Dennis960/Blumy/Firmware/main/configuration_mode_server.c

#include "configuration_mode_server.h"

#include "esp_log.h"
#include "cJSON.h"

#include "plantfi.h"
#include "plantstore.h"
#include "peripherals/sensors.h"
#include "defaults.h"
#include "update.h"
#include "plantmqtt.h"
#include "plantnow.h"

#include "esp_https_ota.h"

#include "index_html.c"

float ota_update_percentage = -1;

// Returns the index_html from index_html.c
esp_err_t get_handler(httpd_req_t *req)
{
    httpd_resp_set_type(req, "text/html");
    httpd_resp_send(req, index_html, sizeof(index_html));
    return ESP_OK;
}

bool get_value(char *content, char *key, char *value, size_t value_size)
{
    // Request bodies are in the form of key=value\nkey2=value2\n
    char *key_start = strstr(content, key);
    if (key_start == NULL)
    {
        return false;
    }
    key_start += strlen(key) + 1;
    char *key_end = strstr(key_start, "\n");
    if (key_end == NULL)
    {
        return false;
    }
    size_t copy_len = key_end - key_start;
    if (copy_len >= value_size)
    {
        copy_len = value_size - 1;
    }
    strncpy(value, key_start, copy_len);
    value[copy_len] = '\0';
    ESP_LOGI("Configuration", "Extracted value for key '%s': '%s'", key, value);
    return true;
}

bool get_values(httpd_req_t *req, char *keys[], char *values[], size_t *sizes, int num_keys)
{
    char content[1000];
    size_t recv_size = MIN(req->content_len, sizeof(content) - 1);
    int ret = httpd_req_recv(req, content, recv_size);
    if (ret <= 0)
    {
        if (ret == HTTPD_SOCK_ERR_TIMEOUT)
        {
            httpd_resp_send_408(req);
        }
        return false;
    }
    content[ret] = '\0'; // Ensure null terminator
    for (int i = 0; i < num_keys; i++)
    {
        if (!get_value(content, keys[i], values[i], sizes[i]))
        {
            return false;
        }
    }
    return true;
}

bool get_single_value(httpd_req_t *req, char *value, size_t buffer_len)
{
    // The entire request body is the value, there is no key and no newline
    size_t recv_size = MIN(req->content_len, buffer_len - 1);
    int ret = httpd_req_recv(req, value, recv_size);
    if (ret <= 0)
    {
        if (ret == HTTPD_SOCK_ERR_TIMEOUT)
        {
            httpd_resp_send_408(req);
        }
        return false;
    }
    value[ret] = '\0'; // Ensure null terminator
    return true;
}

bool is_number(char *content)
{
    for (int i = 0; i < strlen(content); i++)
    {
        if (content[i] < '0' || content[i] > '9')
        {
            return false;
        }
    }
    return true;
}

esp_err_t post_api_connect_handler(httpd_req_t *req)
{
    char ssid[DEFAULT_SSID_MAX_LENGTH];
    char password[DEFAULT_PASSWORD_MAX_LENGTH];
    char *keys[] = {"ssid", "password"};
    char *values[] = {ssid, password};
    size_t sizes[] = {sizeof(ssid), sizeof(password)};
    if (!get_values(req, keys, values, sizes, 2))
    {
        return ESP_FAIL;
    }

    httpd_resp_send(req, "OK", HTTPD_RESP_USE_STRLEN);

    plantfi_configureSta(ssid, password, 5, true);
    return ESP_OK;
}

esp_err_t post_api_reset_handler(httpd_req_t *req)
{
    httpd_resp_send(req, "OK", HTTPD_RESP_USE_STRLEN);

    sensors_playShutdownSound();
    esp_restart();
    return ESP_OK;
}

esp_err_t get_api_networks_handler(httpd_req_t *req)
{
    plantfi_ap_record_t ap_records[20];
    int num_ap_records = 20;
    plantfi_scan_networks(ap_records, &num_ap_records);

    cJSON *root = cJSON_CreateArray();
    for (int i = 0; i < num_ap_records; i++)
    {
        cJSON *ap = cJSON_CreateObject();
        cJSON_AddNumberToObject(ap, "rssi", ap_records[i].rssi);
        cJSON_AddStringToObject(ap, "ssid", ap_records[i].ssid);
        cJSON_AddNumberToObject(ap, "secure", ap_records[i].secure);
        cJSON_AddItemToArray(root, ap);
    }

    char *resp = cJSON_Print(root);
    cJSON_Delete(root);

    httpd_resp_set_type(req, "application/json");
    httpd_resp_send(req, resp, HTTPD_RESP_USE_STRLEN);
    free(resp);
    return ESP_OK;
}

esp_err_t get_api_isConnected_handler(httpd_req_t *req)
{
    plantfi_sta_status_t status = plantfi_get_sta_status();
    char resp[2];
    sprintf(resp, "%d", status);
    httpd_resp_send(req, resp, HTTPD_RESP_USE_STRLEN);
    return ESP_OK;
}

esp_err_t post_api_cloudSetup_mqtt_handler(httpd_req_t *req)
{
    char sensorId[100];
    char server[100];
    char portString[10];
    char username[100];
    char password[100];
    char topic[100];
    char clientId[100];
    char *keys[] = {"sensorId", "server", "port", "username", "password", "topic", "clientId"};
    char *values[] = {sensorId, server, portString, username, password, topic, clientId};
    size_t sizes[] = {sizeof(sensorId), sizeof(server), sizeof(portString), sizeof(username), sizeof(password), sizeof(topic), sizeof(clientId)};
    if (!get_values(req, keys, values, sizes, 7) || !is_number(portString))
    {
        return ESP_FAIL;
    }

    uint32_t port = atoi(portString);

    plantstore_setCloudConfigurationMqtt(sensorId, server, port, username, password, topic, clientId);
    plantmqtt_homeassistant_create_sensor();

    httpd_resp_send(req, "OK", HTTPD_RESP_USE_STRLEN);
    return ESP_OK;
}

esp_err_t post_api_cloudSetup_http_handler(httpd_req_t *req)
{
    char sensorId[100];
    char url[100];
    char auth[100];
    char *keys[] = {"sensorId", "url", "auth"};
    char *values[] = {sensorId, url, auth};
    size_t sizes[] = {sizeof(sensorId), sizeof(url), sizeof(auth)};
    if (!get_values(req, keys, values, sizes, 3))
    {
        return ESP_FAIL;
    }

    plantstore_setCloudConfigurationHttp(sensorId, url, auth);

    httpd_resp_send(req, "OK", HTTPD_RESP_USE_STRLEN);
    return ESP_OK;
}

esp_err_t post_api_cloudSetup_blumy_handler(httpd_req_t *req)
{
    char token[100];
    char url[100];
    char *keys[] = {"token", "url"};
    char *values[] = {token, url};
    size_t sizes[] = {sizeof(token), sizeof(url)};
    if (!get_values(req, keys, values, sizes, 2))
    {
        return ESP_FAIL;
    }

    plantstore_setCloudConfigurationBlumy(token, url);

    httpd_resp_send(req, "OK", HTTPD_RESP_USE_STRLEN);
    return ESP_OK;
}

esp_err_t get_api_cloudSetup_mqtt_handler(httpd_req_t *req)
{
    char sensorId[100];
    char server[100];
    uint32_t port;
    char username[100];
    char password[100];
    char topic[100];
    char clientId[100];

    if (!plantstore_getCloudConfigurationMqtt(sensorId, server, &port, username, password, topic, clientId, sizeof(sensorId), sizeof(server), sizeof(username), sizeof(password), sizeof(topic), sizeof(clientId)))
    {
        httpd_resp_send_404(req);
        return ESP_FAIL;
    }

    cJSON *root = cJSON_CreateObject();
    cJSON_AddStringToObject(root, "sensorId", sensorId);
    cJSON_AddStringToObject(root, "server", server);
    cJSON_AddNumberToObject(root, "port", port);
    cJSON_AddStringToObject(root, "username", username);
    cJSON_AddStringToObject(root, "password", password);
    cJSON_AddStringToObject(root, "topic", topic);
    cJSON_AddStringToObject(root, "clientId", clientId);

    char *resp = cJSON_Print(root);
    cJSON_Delete(root);

    httpd_resp_set_type(req, "application/json");
    httpd_resp_send(req, resp, HTTPD_RESP_USE_STRLEN);
    free(resp);
    return ESP_OK;
}

esp_err_t get_api_cloudSetup_http_handler(httpd_req_t *req)
{
    char sensorId[100];
    char url[100];
    char auth[100];

    if (!plantstore_getCloudConfigurationHttp(sensorId, url, auth, sizeof(sensorId), sizeof(url), sizeof(auth)))
    {
        httpd_resp_send_404(req);
        return ESP_FAIL;
    }

    cJSON *root = cJSON_CreateObject();
    cJSON_AddStringToObject(root, "sensorId", sensorId);
    cJSON_AddStringToObject(root, "url", url);
    cJSON_AddStringToObject(root, "auth", auth);

    char *resp = cJSON_Print(root);
    cJSON_Delete(root);

    httpd_resp_set_type(req, "application/json");
    httpd_resp_send(req, resp, HTTPD_RESP_USE_STRLEN);
    free(resp);
    return ESP_OK;
}

esp_err_t get_api_cloudSetup_blumy_handler(httpd_req_t *req)
{
    char token[100] = "";
    char url[100] = DEFAULT_API_URL;

    plantstore_getCloudConfigurationBlumy(token, url, sizeof(token), sizeof(url));

    cJSON *root = cJSON_CreateObject();
    cJSON_AddStringToObject(root, "token", token);
    cJSON_AddStringToObject(root, "url", url);

    char *resp = cJSON_Print(root);
    cJSON_Delete(root);

    httpd_resp_send(req, resp, HTTPD_RESP_USE_STRLEN);
    free(resp);
    return ESP_OK;
}

esp_err_t post_api_cloudTest_mqtt_handler(httpd_req_t *req)
{
    char sensorId[100];
    char server[100];
    char portString[10];
    char username[100];
    char password[100];
    char topic[100];
    char clientId[100];

    char *keys[] = {"sensorId", "server", "port", "username", "password", "topic", "clientId"};
    char *values[] = {sensorId, server, portString, username, password, topic, clientId};
    size_t sizes[] = {sizeof(sensorId), sizeof(server), sizeof(portString), sizeof(username), sizeof(password), sizeof(topic), sizeof(clientId)};
    if (!get_values(req, keys, values, sizes, 7) || !is_number(portString))
    {
        return ESP_FAIL;
    }

    uint32_t port = atoi(portString);

    const bool connectionOk = plantfi_test_mqtt_connection(sensorId, server, port, username, password, topic, clientId);
    char resp[6];
    sprintf(resp, "%s", connectionOk ? "true" : "false");
    httpd_resp_send(req, resp, HTTPD_RESP_USE_STRLEN);
    return ESP_OK;
}
esp_err_t post_api_cloudTest_http_handler(httpd_req_t *req)
{
    char sensorId[100];
    char url[100];
    char auth[100];

    char *keys[] = {"sensorId", "url", "auth"};
    char *values[] = {sensorId, url, auth};
    size_t sizes[] = {sizeof(sensorId), sizeof(url), sizeof(auth)};
    if (!get_values(req, keys, values, sizes, 3))
    {
        return ESP_FAIL;
    }

    const bool connectionOk = plantfi_test_http_connection(sensorId, url, auth);
    char resp[6];
    sprintf(resp, "%s", connectionOk ? "true" : "false");
    httpd_resp_send(req, resp, HTTPD_RESP_USE_STRLEN);
    return ESP_OK;
}
esp_err_t post_api_cloudTest_blumy_handler(httpd_req_t *req)
{
    char token[100];
    char url[100];
    char *keys[] = {"token", "url"};
    char *values[] = {token, url};
    size_t sizes[] = {sizeof(token), sizeof(url)};
    if (!get_values(req, keys, values, sizes, 2))
    {
        return ESP_FAIL;
    }

    const bool connectionOk = plantfi_test_blumy_connection(token, url);
    char resp[6];
    sprintf(resp, "%s", connectionOk ? "true" : "false");
    httpd_resp_send(req, resp, HTTPD_RESP_USE_STRLEN);
    return ESP_OK;
}

esp_err_t post_api_cloudDisable_mqtt_handler(httpd_req_t *req)
{
    plantstore_resetCloudConfigurationMqtt();
    httpd_resp_send(req, "OK", HTTPD_RESP_USE_STRLEN);
    return ESP_OK;
}

esp_err_t post_api_cloudDisable_http_handler(httpd_req_t *req)
{
    plantstore_resetCloudConfigurationHttp();
    httpd_resp_send(req, "OK", HTTPD_RESP_USE_STRLEN);
    return ESP_OK;
}

esp_err_t post_api_cloudDisable_blumy_handler(httpd_req_t *req)
{
    plantstore_resetCloudConfigurationBlumy();
    httpd_resp_send(req, "OK", HTTPD_RESP_USE_STRLEN);
    return ESP_OK;
}

esp_err_t post_api_timeouts_sleep_handler(httpd_req_t *req)
{
    char timoutString[10];
    if (!get_single_value(req, timoutString, 10) || !is_number(timoutString))
    {
        return ESP_FAIL;
    }

    int32_t timeout;
    sscanf(timoutString, "%ld", &timeout);

    plantstore_setSensorTimeoutSleepMs(timeout);

    httpd_resp_send(req, "OK", HTTPD_RESP_USE_STRLEN);
    return ESP_OK;
}

esp_err_t get_api_timeouts_sleep_handler(httpd_req_t *req)
{
    uint64_t timeout = DEFAULT_SENSOR_TIMEOUT_SLEEP_MS;
    plantstore_getSensorTimeoutSleepMs(&timeout);

    char resp[15];
    sprintf(resp, "%llu", timeout);
    httpd_resp_send(req, resp, HTTPD_RESP_USE_STRLEN);
    return ESP_OK;
}

esp_err_t get_api_timeouts_configurationMode_handler(httpd_req_t *req)
{
    int32_t timeout = DEFAULT_CONFIGURATION_MODE_TIMEOUT_MS;
    plantstore_getConfigurationModeTimeoutMs(&timeout);

    char resp[15];
    sprintf(resp, "%ld", timeout);
    httpd_resp_send(req, resp, HTTPD_RESP_USE_STRLEN);
    return ESP_OK;
}

esp_err_t post_api_timeouts_configurationMode_handler(httpd_req_t *req)
{
    char timoutString[10];
    if (!get_single_value(req, timoutString, 10) || !is_number(timoutString))
    {
        return ESP_FAIL;
    }

    int32_t timeout;
    sscanf(timoutString, "%ld", &timeout);

    plantstore_setConfigurationModeTimeoutMs(timeout);

    httpd_resp_send(req, "OK", HTTPD_RESP_USE_STRLEN);
    return ESP_OK;
}

esp_err_t get_api_timeouts_wdt_handler(httpd_req_t *req)
{
    uint64_t timeout = DEFAULT_WATCHDOG_TIMEOUT_MS;
    plantstore_getWatchdogTimeoutMs(&timeout);

    char resp[15];
    sprintf(resp, "%llu", timeout);
    httpd_resp_send(req, resp, HTTPD_RESP_USE_STRLEN);
    return ESP_OK;
}

esp_err_t post_api_timeouts_wdt_handler(httpd_req_t *req)
{
    char timoutString[10];
    if (!get_single_value(req, timoutString, 10) || !is_number(timoutString))
    {
        return ESP_FAIL;
    }

    uint64_t timeout;
    sscanf(timoutString, "%llu", &timeout);

    plantstore_setWatchdogTimeoutMs(timeout);

    httpd_resp_send(req, "OK", HTTPD_RESP_USE_STRLEN);
    return ESP_OK;
}

esp_err_t get_api_timeouts_mqtt_message_handler(httpd_req_t *req)
{
    uint64_t timeout = DEFAULT_MQTT_MESSAGE_TIMEOUT_MS;
    plantstore_getMqttMessageTimeoutMs(&timeout);

    char resp[15];
    sprintf(resp, "%llu", timeout);
    httpd_resp_send(req, resp, HTTPD_RESP_USE_STRLEN);
    return ESP_OK;
}

esp_err_t post_api_timeouts_mqtt_message_handler(httpd_req_t *req)
{
    char timoutString[10];
    if (!get_single_value(req, timoutString, 10) || !is_number(timoutString))
    {
        return ESP_FAIL;
    }

    uint64_t timeout;
    sscanf(timoutString, "%llu", &timeout);

    plantstore_setMqttMessageTimeoutMs(timeout);

    httpd_resp_send(req, "OK", HTTPD_RESP_USE_STRLEN);
    return ESP_OK;
}

esp_err_t get_api_led_brightness_handler(httpd_req_t *req)
{
    uint8_t brightness = DEFAULT_LED_BRIGHTNESS;
    plantstore_getLedBrightness(&brightness);

    char resp[4];
    sprintf(resp, "%d", brightness);
    httpd_resp_send(req, resp, HTTPD_RESP_USE_STRLEN);
    return ESP_OK;
}

esp_err_t post_api_led_brightness_handler(httpd_req_t *req)
{
    char brightnessString[10];
    if (!get_single_value(req, brightnessString, 10))
    {
        ESP_LOGI("DEBUG", "1");
        return ESP_FAIL;
    }
    ESP_LOGI("DEBUG", "%s", brightnessString);
    if (!is_number(brightnessString))
    {
        ESP_LOGI("DEBUG", "2");
        return ESP_FAIL;
    }

    uint8_t brightness;
    sscanf(brightnessString, "%hhu", &brightness);

    plantstore_setLedBrightness(brightness);

    httpd_resp_send(req, "OK", HTTPD_RESP_USE_STRLEN);
    return ESP_OK;
}

esp_err_t get_api_update_percentage_handler(httpd_req_t *req)
{
    char resp[10];
    sprintf(resp, "%.2f", ota_update_percentage);
    httpd_resp_send(req, resp, HTTPD_RESP_USE_STRLEN);
    return ESP_OK;
}

esp_err_t get_api_connectedNetwork_handler(httpd_req_t *req)
{
    char ssid[DEFAULT_SSID_MAX_LENGTH];
    char password[DEFAULT_PASSWORD_MAX_LENGTH];

    if (!plantstore_getWifiCredentials(ssid, password, sizeof(ssid), sizeof(password)))
    {
        httpd_resp_send_404(req);
        return ESP_FAIL;
    }
    plantfi_sta_status_t status = plantfi_get_sta_status();
    int8_t rssi = plantfi_getRssi();

    cJSON *root = cJSON_CreateObject();
    cJSON_AddStringToObject(root, "ssid", ssid);
    // cJSON_AddStringToObject(root, "password", password);
    cJSON_AddNumberToObject(root, "status", status);
    cJSON_AddNumberToObject(root, "rssi", rssi);

    char *resp = cJSON_Print(root);
    cJSON_Delete(root);

    httpd_resp_set_type(req, "application/json");
    httpd_resp_send(req, resp, HTTPD_RESP_USE_STRLEN);
    free(resp);
    return ESP_OK;
}

esp_err_t get_api_sensor_data_handler(httpd_req_t *req)
{
    sensors_full_data_t sensors_data;
    sensors_full_read(&sensors_data);

    cJSON *root = cJSON_CreateObject();
    cJSON_AddNumberToObject(root, "temperature", sensors_data.temperature);
    cJSON_AddNumberToObject(root, "humidity", sensors_data.humidity);
    cJSON_AddNumberToObject(root, "light", sensors_data.light);
    cJSON_AddNumberToObject(root, "moisture", sensors_data.moisture_measurement);
    cJSON_AddNumberToObject(root, "voltage", sensors_data.voltage);

    char *resp = cJSON_Print(root);
    cJSON_Delete(root);

    httpd_resp_set_type(req, "application/json");
    httpd_resp_send(req, resp, HTTPD_RESP_USE_STRLEN);
    free(resp);
    return ESP_OK;
}

esp_err_t post_api_factoryReset_handler(httpd_req_t *req)
{
    httpd_resp_send(req, "OK", HTTPD_RESP_USE_STRLEN);

    plantstore_factoryReset();
    esp_restart();
    return ESP_OK;
}

esp_err_t post_api_update_firmware_handler(httpd_req_t *req)
{
    char url[100];
    char *keys[] = {"url"};
    char *values[] = {url};
    size_t sizes[] = {sizeof(url)};
    if (!get_values(req, keys, values, sizes, 1))
    {
        return ESP_FAIL;
    }

    plantstore_setFirmwareUpdateUrl(url);
    ota_update_percentage = 0;

    httpd_resp_send(req, "OK", HTTPD_RESP_USE_STRLEN);
    update_updateFirmware(&ota_update_percentage);
    return ESP_OK;
}

esp_err_t get_api_update_firmware_handler(httpd_req_t *req)
{
    char url[100] = DEFAULT_FIRMWARE_UPDATE_URL;
    plantstore_getFirmwareUpdateUrl(url, sizeof(url));

    cJSON *root = cJSON_CreateObject();
    cJSON_AddStringToObject(root, "url", url);

    char *resp = cJSON_Print(root);
    cJSON_Delete(root);

    httpd_resp_set_type(req, "application/json");
    httpd_resp_send(req, resp, HTTPD_RESP_USE_STRLEN);
    free(resp);
    return ESP_OK;
}

esp_err_t post_api_update_check_handler(httpd_req_t *req)
{
    char url[100];
    char *keys[] = {"url"};
    char *values[] = {url};
    size_t sizes[] = {sizeof(url)};
    if (!get_values(req, keys, values, sizes, 1))
    {
        return ESP_FAIL;
    }

    esp_http_client_config_t config = {
        .url = url,
        .method = HTTP_METHOD_HEAD,
        .timeout_ms = 10000,
        .cert_pem = NULL,
    };
    esp_http_client_handle_t client = esp_http_client_init(&config);
    if (client == NULL)
    {
        ESP_LOGE("HTTP", "Failed to initialize HTTP client");
        return ESP_FAIL;
    }
    esp_err_t err = esp_http_client_perform(client);
    if (err != ESP_OK)
    {
        ESP_LOGE("HTTP", "Failed to perform HTTP request (%s)", esp_err_to_name(err));
        return err;
    }
    int status_code = esp_http_client_get_status_code(client);
    int content_length = esp_http_client_get_content_length(client);
    ESP_LOGI("HTTP", "Status code: %d, Content length: %d", status_code, content_length);

    char resp[6];
    sprintf(resp, "%s", status_code == 200 ? "true" : "false");
    httpd_resp_send(req, resp, HTTPD_RESP_USE_STRLEN);

    esp_http_client_cleanup(client);
    return ESP_OK;
}

esp_err_t get_api_firmware_version_handler(httpd_req_t *req)
{
    uint64_t version = FIRMWARE_VERSION;
    char resp[20];
    sprintf(resp, "%llu", version);
    httpd_resp_send(req, resp, HTTPD_RESP_USE_STRLEN);
    return ESP_OK;
}

esp_err_t plantnow_hasReceivedPeerMacHandler(httpd_req_t *req)
{
    uint8_t *mac = plantnow_getPeerMac();
    char resp[20]; // Enough for "xx:xx:xx:xx:xx:xx"
    if (mac == NULL)
    {
        sprintf(resp, "\"\"");
    }
    else
    {
        sprintf(resp, "\"%02x:%02x:%02x:%02x:%02x:%02x\"",
                mac[0], mac[1], mac[2], mac[3], mac[4], mac[5]);
    }
    httpd_resp_set_type(req, "application/json");
    httpd_resp_send(req, resp, HTTPD_RESP_USE_STRLEN);
    return ESP_OK;
}

esp_err_t plantnow_sendWifiCredentialsHandler(httpd_req_t *req)
{
    if (plantnow_getPeerMac() == NULL)
    {
        httpd_resp_send_err(req, HTTPD_500_INTERNAL_SERVER_ERROR, "ERROR: No peer MAC address received");
        return ESP_FAIL;
    }
    if (!plantstore_getWifiCredentials(NULL, NULL, 0, 0))
    {
        httpd_resp_send_err(req, HTTPD_500_INTERNAL_SERVER_ERROR, "ERROR: No WiFi credentials stored");
        return ESP_FAIL;
    }
    if (plantnow_sendWifiCredentials(true) != ESP_OK)
    {
        httpd_resp_send_err(req, HTTPD_500_INTERNAL_SERVER_ERROR, "ERROR: Failed to send WiFi credentials");
        return ESP_FAIL;
    }

    httpd_resp_send(req, "OK", HTTPD_RESP_USE_STRLEN);
    return ESP_OK;
}

esp_err_t plantnow_sendCloudSetup_blumyHandler(httpd_req_t *req)
{
    char token[100];
    char url[100];
    char *keys[] = {"token", "url"};
    char *values[] = {token, url};
    size_t sizes[] = {sizeof(token), sizeof(url)};
    if (!get_values(req, keys, values, sizes, 2))
    {
        return ESP_FAIL;
    }
    if (plantnow_getPeerMac() == NULL)
    {
        httpd_resp_send_err(req, HTTPD_500_INTERNAL_SERVER_ERROR, "ERROR: No peer MAC address received");
        return ESP_FAIL;
    }
    cloud_setup_blumy_t setup;
    strcpy(setup.token, token);
    strcpy(setup.url, url);
    if (plantnow_sendCloudSetupBlumy(&setup, true) != ESP_OK)
    {
        httpd_resp_send_err(req, HTTPD_500_INTERNAL_SERVER_ERROR, "ERROR: Failed to send Blumy cloud setup");
        return ESP_FAIL;
    }

    httpd_resp_send(req, "OK", HTTPD_RESP_USE_STRLEN);
    return ESP_OK;
}

httpd_uri_t post_api_connect = {
    .uri = "/api/connect",
    .method = HTTP_POST,
    .handler = post_api_connect_handler,
    .user_ctx = NULL};

httpd_uri_t post_api_reset = {
    .uri = "/api/reset",
    .method = HTTP_POST,
    .handler = post_api_reset_handler,
    .user_ctx = NULL};

httpd_uri_t get_api_networks = {
    .uri = "/api/networks",
    .method = HTTP_GET,
    .handler = get_api_networks_handler,
    .user_ctx = NULL};

httpd_uri_t get_api_isConnected = {
    .uri = "/api/isConnected",
    .method = HTTP_GET,
    .handler = get_api_isConnected_handler,
    .user_ctx = NULL};

httpd_uri_t post_api_cloudSetup_mqtt = {
    .uri = "/api/cloudSetup/mqtt",
    .method = HTTP_POST,
    .handler = post_api_cloudSetup_mqtt_handler,
    .user_ctx = NULL};
httpd_uri_t post_api_cloudSetup_http = {
    .uri = "/api/cloudSetup/http",
    .method = HTTP_POST,
    .handler = post_api_cloudSetup_http_handler,
    .user_ctx = NULL};
httpd_uri_t post_api_cloudSetup_blumy = {
    .uri = "/api/cloudSetup/blumy",
    .method = HTTP_POST,
    .handler = post_api_cloudSetup_blumy_handler,
    .user_ctx = NULL};

httpd_uri_t get_api_cloudSetup_mqtt = {
    .uri = "/api/cloudSetup/mqtt",
    .method = HTTP_GET,
    .handler = get_api_cloudSetup_mqtt_handler,
    .user_ctx = NULL};
httpd_uri_t get_api_cloudSetup_http = {
    .uri = "/api/cloudSetup/http",
    .method = HTTP_GET,
    .handler = get_api_cloudSetup_http_handler,
    .user_ctx = NULL};
httpd_uri_t get_api_cloudSetup_blumy = {
    .uri = "/api/cloudSetup/blumy",
    .method = HTTP_GET,
    .handler = get_api_cloudSetup_blumy_handler,
    .user_ctx = NULL};

httpd_uri_t post_api_cloudTest_mqtt = {
    .uri = "/api/cloudTest/mqtt",
    .method = HTTP_POST,
    .handler = post_api_cloudTest_mqtt_handler,
    .user_ctx = NULL};
httpd_uri_t post_api_cloudTest_http = {
    .uri = "/api/cloudTest/http",
    .method = HTTP_POST,
    .handler = post_api_cloudTest_http_handler,
    .user_ctx = NULL};
httpd_uri_t post_api_cloudTest_blumy = {
    .uri = "/api/cloudTest/blumy",
    .method = HTTP_POST,
    .handler = post_api_cloudTest_blumy_handler,
    .user_ctx = NULL};

httpd_uri_t post_api_cloudDisable_mqtt = {
    .uri = "/api/cloudDisable/mqtt",
    .method = HTTP_POST,
    .handler = post_api_cloudDisable_mqtt_handler,
    .user_ctx = NULL};
httpd_uri_t post_api_cloudDisable_http = {
    .uri = "/api/cloudDisable/http",
    .method = HTTP_POST,
    .handler = post_api_cloudDisable_http_handler,
    .user_ctx = NULL};
httpd_uri_t post_api_cloudDisable_blumy = {
    .uri = "/api/cloudDisable/blumy",
    .method = HTTP_POST,
    .handler = post_api_cloudDisable_blumy_handler,
    .user_ctx = NULL};

httpd_uri_t post_api_timeouts_sleep = {
    .uri = "/api/timeouts/sleep",
    .method = HTTP_POST,
    .handler = post_api_timeouts_sleep_handler,
    .user_ctx = NULL};

httpd_uri_t get_api_timeouts_sleep = {
    .uri = "/api/timeouts/sleep",
    .method = HTTP_GET,
    .handler = get_api_timeouts_sleep_handler,
    .user_ctx = NULL};

httpd_uri_t get_api_timeouts_configurationMode = {
    .uri = "/api/timeouts/configurationMode",
    .method = HTTP_GET,
    .handler = get_api_timeouts_configurationMode_handler,
    .user_ctx = NULL};

httpd_uri_t post_api_timeouts_configurationMode = {
    .uri = "/api/timeouts/configurationMode",
    .method = HTTP_POST,
    .handler = post_api_timeouts_configurationMode_handler,
    .user_ctx = NULL};

httpd_uri_t get_api_timeouts_wdt = {
    .uri = "/api/timeouts/wdt",
    .method = HTTP_GET,
    .handler = get_api_timeouts_wdt_handler,
    .user_ctx = NULL};

httpd_uri_t post_api_timeouts_wdt = {
    .uri = "/api/timeouts/wdt",
    .method = HTTP_POST,
    .handler = post_api_timeouts_wdt_handler,
    .user_ctx = NULL};

httpd_uri_t get_api_timeouts_mqtt_message = {
    .uri = "/api/timeouts/mqttMessage",
    .method = HTTP_GET,
    .handler = get_api_timeouts_mqtt_message_handler,
    .user_ctx = NULL};

httpd_uri_t post_api_timeouts_mqtt_message = {
    .uri = "/api/timeouts/mqttMessage",
    .method = HTTP_POST,
    .handler = post_api_timeouts_mqtt_message_handler,
    .user_ctx = NULL};

httpd_uri_t post_api_led_brightness = {
    .uri = "/api/led/brightness",
    .method = HTTP_POST,
    .handler = post_api_led_brightness_handler,
    .user_ctx = NULL};

httpd_uri_t get_api_led_brightness = {
    .uri = "/api/led/brightness",
    .method = HTTP_GET,
    .handler = get_api_led_brightness_handler,
    .user_ctx = NULL};

httpd_uri_t get_api_update_percentage = {
    .uri = "/api/update/percentage",
    .method = HTTP_GET,
    .handler = get_api_update_percentage_handler,
    .user_ctx = NULL};

httpd_uri_t get_api_connectedNetwork = {
    .uri = "/api/connectedNetwork",
    .method = HTTP_GET,
    .handler = get_api_connectedNetwork_handler,
    .user_ctx = NULL};

httpd_uri_t get_api_sensorData = {
    .uri = "/api/sensor/data",
    .method = HTTP_GET,
    .handler = get_api_sensor_data_handler,
    .user_ctx = NULL};

httpd_uri_t post_api_factoryReset = {
    .uri = "/api/factoryReset",
    .method = HTTP_POST,
    .handler = post_api_factoryReset_handler,
    .user_ctx = NULL};

httpd_uri_t post_api_update_firmware = {
    .uri = "/api/update/firmware",
    .method = HTTP_POST,
    .handler = post_api_update_firmware_handler,
    .user_ctx = NULL};

httpd_uri_t get_api_update_firmware = {
    .uri = "/api/update/firmware",
    .method = HTTP_GET,
    .handler = get_api_update_firmware_handler,
    .user_ctx = NULL};

httpd_uri_t post_api_update_check = {
    .uri = "/api/update/check",
    .method = HTTP_POST,
    .handler = post_api_update_check_handler,
    .user_ctx = NULL};

httpd_uri_t get_api_firmware_version = {
    .uri = "/api/firmware/version",
    .method = HTTP_GET,
    .handler = get_api_firmware_version_handler,
    .user_ctx = NULL};

httpd_uri_t get_api_plantnow_hasReceivedPeerMac = {
    .uri = "/api/plantnow/hasReceivedPeerMac",
    .method = HTTP_GET,
    .handler = plantnow_hasReceivedPeerMacHandler,
    .user_ctx = NULL};

httpd_uri_t post_api_plantnow_sendWifiCredentials = {
    .uri = "/api/plantnow/sendWifiCredentials",
    .method = HTTP_POST,
    .handler = plantnow_sendWifiCredentialsHandler,
    .user_ctx = NULL};

httpd_uri_t post_api_plantnow_sendCloudSetup_blumy = {
    .uri = "/api/plantnow/sendCloudSetup/blumy",
    .method = HTTP_POST,
    .handler = plantnow_sendCloudSetup_blumyHandler,
    .user_ctx = NULL};

httpd_uri_t get = {
    .uri = "*",
    .method = HTTP_GET,
    .handler = get_handler,
    .user_ctx = NULL};

void register_uri_handlers(httpd_handle_t server)
{
    httpd_register_uri_handler(server, &post_api_connect);
    httpd_register_uri_handler(server, &post_api_reset);
    httpd_register_uri_handler(server, &get_api_networks);
    httpd_register_uri_handler(server, &get_api_isConnected);
    httpd_register_uri_handler(server, &post_api_cloudSetup_mqtt);
    httpd_register_uri_handler(server, &post_api_cloudSetup_http);
    httpd_register_uri_handler(server, &post_api_cloudSetup_blumy);
    httpd_register_uri_handler(server, &get_api_cloudSetup_mqtt);
    httpd_register_uri_handler(server, &get_api_cloudSetup_http);
    httpd_register_uri_handler(server, &get_api_cloudSetup_blumy);
    httpd_register_uri_handler(server, &post_api_cloudTest_mqtt);
    httpd_register_uri_handler(server, &post_api_cloudTest_http);
    httpd_register_uri_handler(server, &post_api_cloudTest_blumy);
    httpd_register_uri_handler(server, &post_api_cloudDisable_mqtt);
    httpd_register_uri_handler(server, &post_api_cloudDisable_http);
    httpd_register_uri_handler(server, &post_api_cloudDisable_blumy);
    httpd_register_uri_handler(server, &post_api_timeouts_sleep);
    httpd_register_uri_handler(server, &get_api_timeouts_sleep);
    httpd_register_uri_handler(server, &get_api_timeouts_configurationMode);
    httpd_register_uri_handler(server, &post_api_timeouts_configurationMode);
    httpd_register_uri_handler(server, &get_api_timeouts_wdt);
    httpd_register_uri_handler(server, &post_api_timeouts_wdt);
    httpd_register_uri_handler(server, &get_api_timeouts_mqtt_message);
    httpd_register_uri_handler(server, &post_api_timeouts_mqtt_message);
    httpd_register_uri_handler(server, &post_api_led_brightness);
    httpd_register_uri_handler(server, &get_api_led_brightness);
    httpd_register_uri_handler(server, &get_api_update_percentage);
    httpd_register_uri_handler(server, &get_api_connectedNetwork);
    httpd_register_uri_handler(server, &get_api_sensorData);
    httpd_register_uri_handler(server, &post_api_factoryReset);
    httpd_register_uri_handler(server, &post_api_update_firmware);
    httpd_register_uri_handler(server, &get_api_update_firmware);
    httpd_register_uri_handler(server, &post_api_update_check);
    httpd_register_uri_handler(server, &get_api_firmware_version);
    httpd_register_uri_handler(server, &get_api_plantnow_hasReceivedPeerMac);
    httpd_register_uri_handler(server, &post_api_plantnow_sendWifiCredentials);
    httpd_register_uri_handler(server, &post_api_plantnow_sendCloudSetup_blumy);

    // Every other get request returns index.html
    httpd_register_uri_handler(server, &get);
}

httpd_handle_t start_webserver()
{
    ESP_LOGI("HTTP", "Starting HTTP server");
    /* Empty handle to esp_http_server */
    httpd_handle_t server = NULL;

    /* Generate default configuration */
    httpd_config_t config = HTTPD_DEFAULT_CONFIG();
    config.uri_match_fn = httpd_uri_match_wildcard;
    config.max_uri_handlers = 50;

    /* Start the httpd server */
    ESP_ERROR_CHECK(httpd_start(&server, &config));
    register_uri_handlers(server);
    /* If server failed to start, handle will be NULL */
    return server;
}

/* Function for stopping the webserver */
void stop_webserver(httpd_handle_t server)
{
    if (server)
    {
        /* Stop the httpd server */
        httpd_stop(server);
    }
}
