Dennis960/Blumy/Firmware/main/configuration_mode_server.h

#pragma once

#include "esp_http_server.h"

/* Function for starting the webserver */
httpd_handle_t start_webserver();
/* Function for stopping the webserver */
void stop_webserver(httpd_handle_t server);
